KazmirFahrier/ATX-24-Pin-Inline-Power-Monitoring-Board/ATX.kicad_sch

## KiCad design ATX.kicad_sch (2026-09-09)

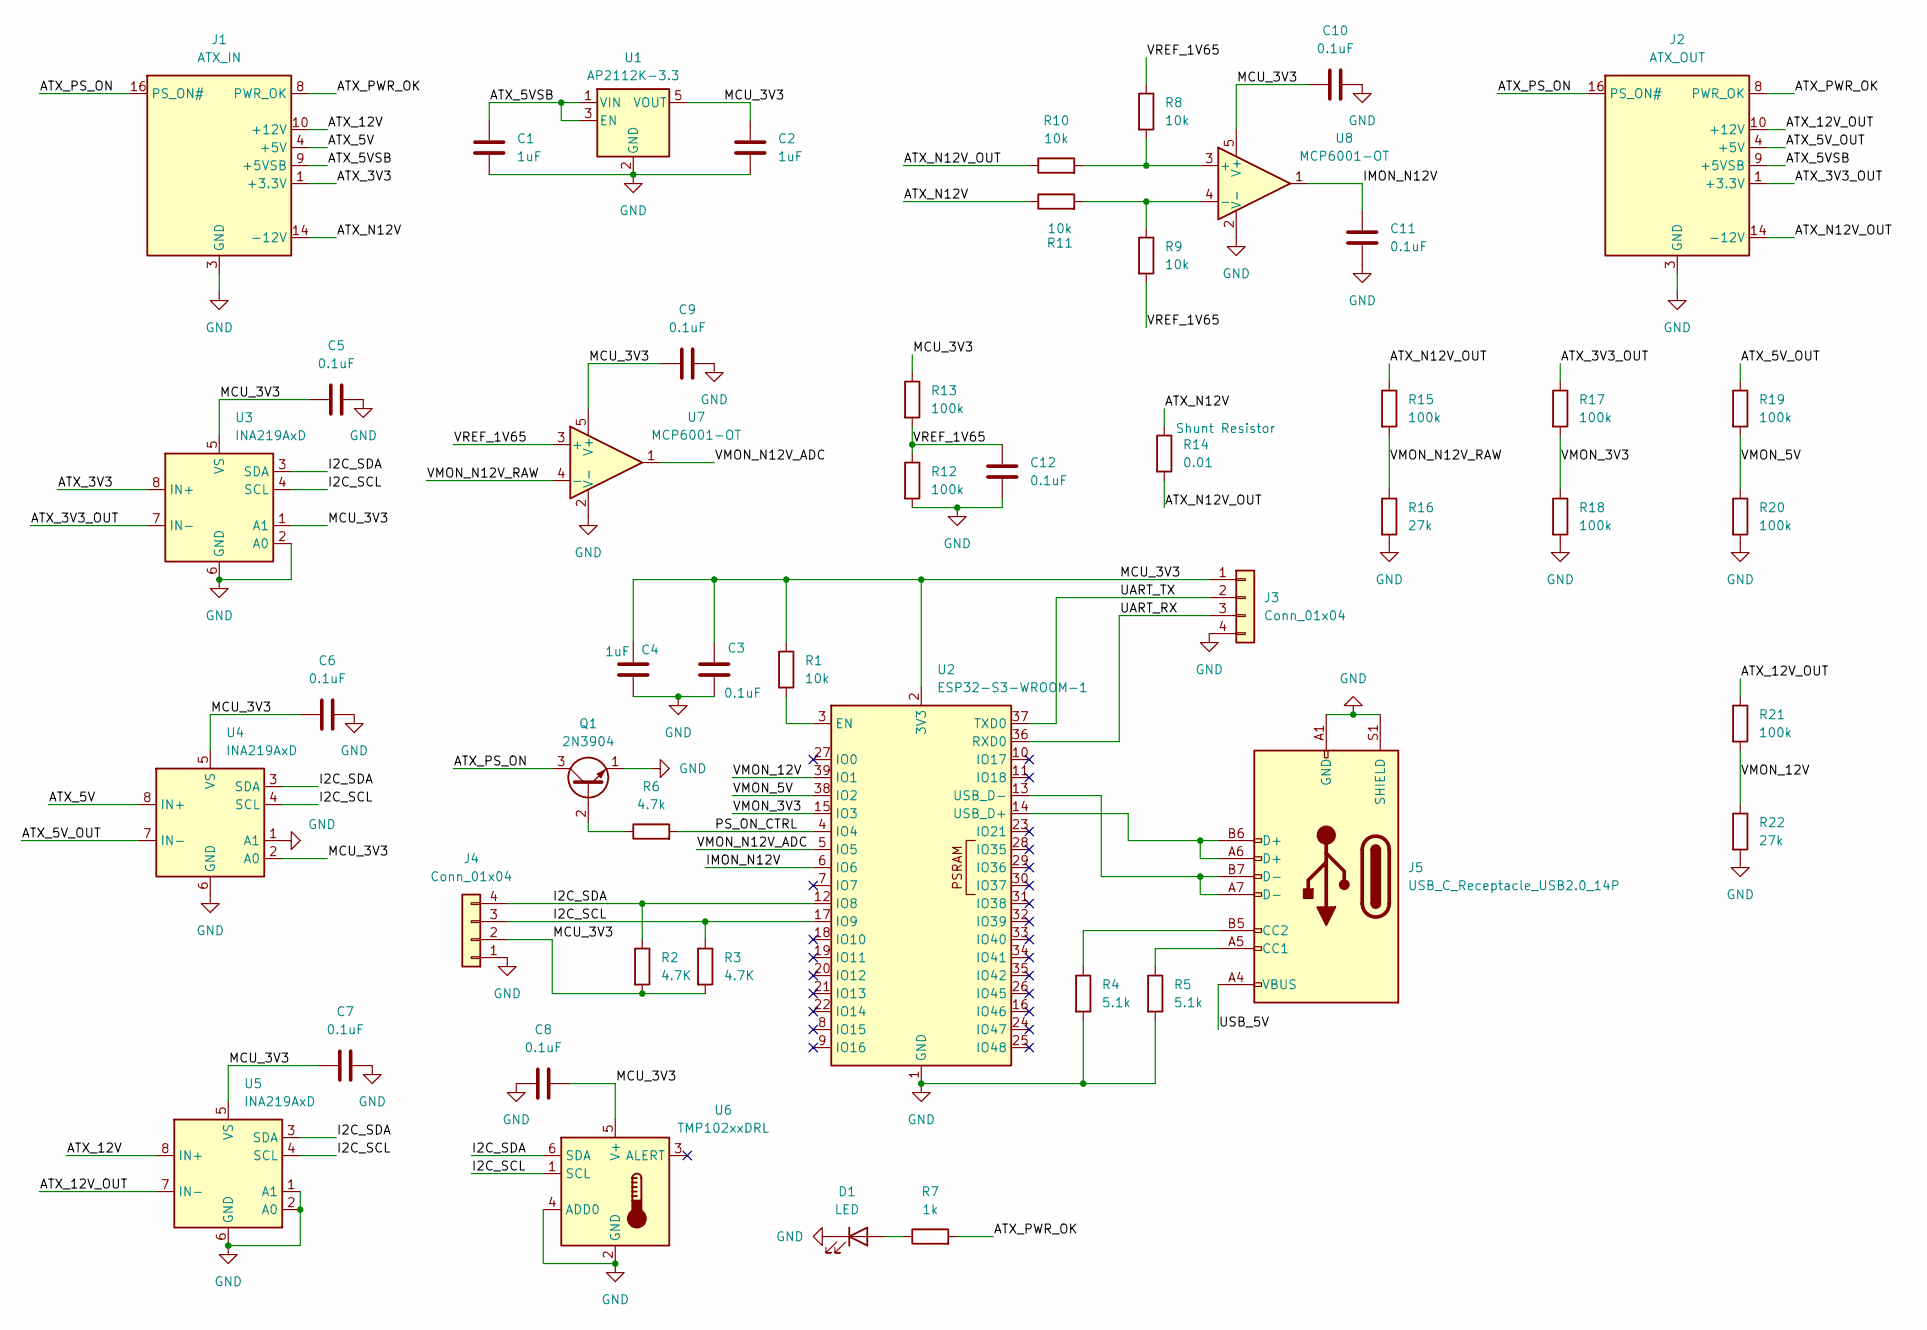
[picture p2: schematic ATX.kicad_sch]

Parts:
C1, C2, C4: 1uF
C3, C5, C6, C7, C8, C9, C10, C11, C12: 0.1uF
D1: LED
J1: ATX_IN
J2: ATX_OUT
J3, J4: Conn_01x04
J5: USB_C_Receptacle_USB2.0_14P
Q1: 2N3904; TO-92_Inline
R1, R8, R9, R10, R11: 10k
R2, R3: 4.7K
R4, R5: 5.1k
R6: 4.7k
R7: 1k
R12, R13, R15, R17, R18, R19, R20, R21: 100k
R14: 0.01
R16, R22: 27k
U1: AP2112K-3.3; SOT-23-5
U2: ESP32-S3-WROOM-1
U3, U4, U5: INA219AxD; SOIC-8_3.9x4.9mm_P1.27mm
U6: TMP102xxDRL; SOT-563
U7, U8: MCP6001-OT; SOT-23-5

Connections:
ATX_3V3: J1.1 (+3.3V), J1.2 (+3.3V), J1.12 (+3.3V), J1.13 (+3.3V), U3.8 (IN+)
ATX_3V3_OUT: J2.1 (+3.3V), J2.2 (+3.3V), J2.12 (+3.3V), J2.13 (+3.3V), R17.1, U3.7 (IN-)
ATX_5V: J1.4 (+5V), J1.6 (+5V), J1.21 (+5V), J1.22 (+5V), J1.23 (+5V), U4.8 (IN+)
ATX_5VSB: C1.1, J1.9 (+5VSB), J2.9 (+5VSB), U1.1 (VIN), U1.3 (EN)
ATX_5V_OUT: J2.4 (+5V), J2.6 (+5V), J2.21 (+5V), J2.22 (+5V), J2.23 (+5V), R19.1, U4.7 (IN-)
ATX_12V: J1.10 (+12V), J1.11 (+12V), U5.8 (IN+)
ATX_12V_OUT: J2.10 (+12V), J2.11 (+12V), R21.1, U5.7 (IN-)
ATX_N12V: J1.14 (-12V), R11.1, R14.1
ATX_N12V_OUT: J2.14 (-12V), R10.1, R14.2, R15.1
ATX_PS_ON: J1.16 (PS_ON#), J2.16 (PS_ON#), Q1.3 (C)
ATX_PWR_OK: J1.8 (PWR_OK), J2.8 (PWR_OK), R7.2
GND: C1.2, C2.2, C3.2, C4.2, C5.2, C6.2, C7.2, C8.1, C9.2, C10.2, C11.2, C12.2, D1.1 (K), J1.3 (GND), J1.5 (GND), J1.7 (GND), J1.15 (GND), J1.17 (GND), J1.18 (GND), J1.19 (GND), J1.24 (GND), J2.3 (GND), J2.5 (GND), J2.7 (GND), J2.15 (GND), J2.17 (GND), J2.18 (GND), J2.19 (GND), J2.24 (GND), J3.4, J4.1, J5.A1 (GND), J5.A12 (GND), J5.B1 (GND), J5.B12 (GND), J5.S1 (SHIELD), Q1.1 (E), R4.2, R5.2, R12.2, R16.2, R18.2, R20.2, R22.2, U1.2 (GND), U2.1 (GND), U2.40 (GND), U2.41 (GND), U3.2 (A0), U3.6 (GND), U4.1 (A1), U4.6 (GND), U5.1 (A1), U5.2 (A0), U5.6 (GND), U6.2 (GND), U6.4 (ADD0), U7.2 (V-), U8.2 (V-)
I2C_SCL: J4.3, R3.1, U2.17 (IO9), U3.4 (SCL), U4.4 (SCL), U5.4 (SCL), U6.1 (SCL)
I2C_SDA: J4.4, R2.1, U2.12 (IO8), U3.3 (SDA), U4.3 (SDA), U5.3 (SDA), U6.6 (SDA)
IMON_N12V: C11.1, U2.6 (IO6), U8.1
MCU_3V3: C2.1, C3.1, C4.1, C5.1, C6.1, C7.1, C8.2, C9.1, C10.1, J3.1, J4.2, R1.1, R2.2, R3.2, R13.1, U1.5 (VOUT), U2.2 (3V3), U3.1 (A1), U3.5 (VS), U4.2 (A0), U4.5 (VS), U5.5 (VS), U6.5 (V+), U7.5 (V+), U8.5 (V+)
unnamed: D1.2 (A), R7.1
unnamed: J5.A5 (CC1), R5.1
unnamed: J5.A6 (D+), J5.B6 (D+), U2.14 (USB_D+)
unnamed: J5.A7 (D-), J5.B7 (D-), U2.13 (USB_D-)
unnamed: J5.B5 (CC2), R4.1
unnamed: Q1.2 (B), R6.1
unnamed: R1.2, U2.3 (EN)
unnamed: R8.2, R10.2, U8.3 (+)
unnamed: R9.1, R11.2, U8.4 (-)
PS_ON_CTRL: R6.2, U2.4 (IO4)
UART_RX: J3.3, U2.36 (RXD0)
UART_TX: J3.2, U2.37 (TXD0)
USB_5V: J5.A4 (VBUS), J5.A9 (VBUS), J5.B4 (VBUS), J5.B9 (VBUS)
VMON_3V3: R17.2, R18.1, U2.15 (IO3)
VMON_5V: R19.2, R20.1, U2.38 (IO2)
VMON_12V: R21.2, R22.1, U2.39 (IO1)
VMON_N12V_ADC: U2.5 (IO5), U7.1
VMON_N12V_RAW: R15.2, R16.1, U7.4 (-)
VREF_1V65: C12.1, R8.1, R9.2, R12.1, R13.2, U7.3 (+)
